mlon/keyboard/src/midi.h

#pragma once

#include <stdbool.h>
#include <stdlib.h>

void initMidi(void);

void sendByte(unsigned char data);
void sendChannelPressure(unsigned char channelPressure);
void sendKey(unsigned char row, unsigned char col, bool on, unsigned int delay);
